chrisdalke/pumpkin-carving-robot/hardware/z_axis_400mm.SLDPRT

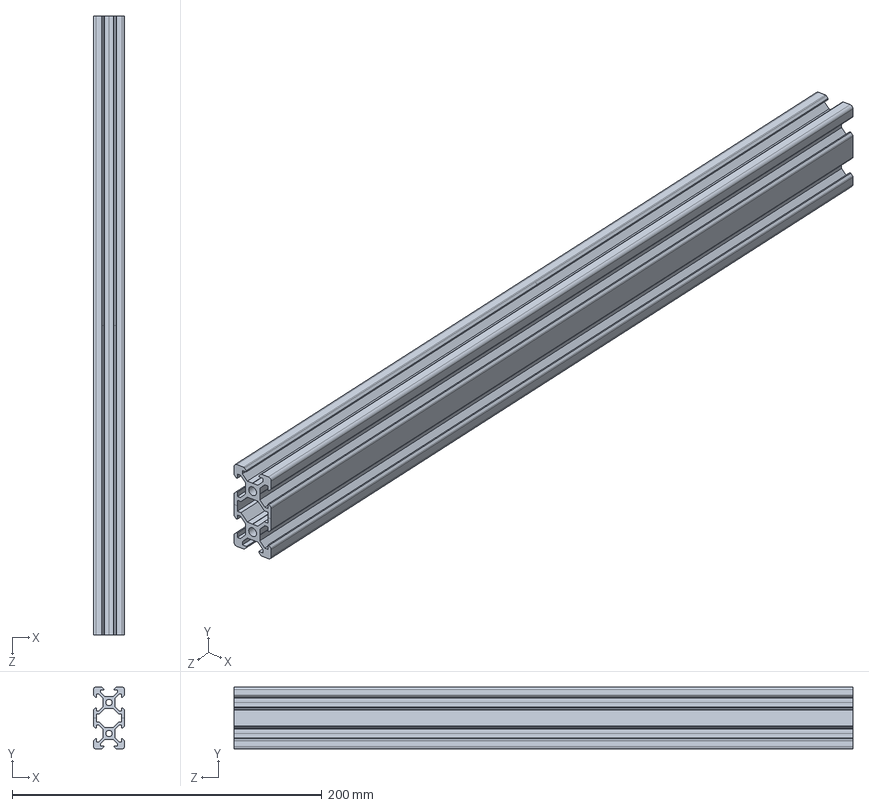
[picture p19: CAD file, 2022-10-28]
hardware/z_axis_400mm.SLDPRT
20.0 x 40.0 x 400.0 mm
