chrisdalke/pumpkin-carving-robot/hardware/8020/8020-1010-BLACK X 8.SLDPRT

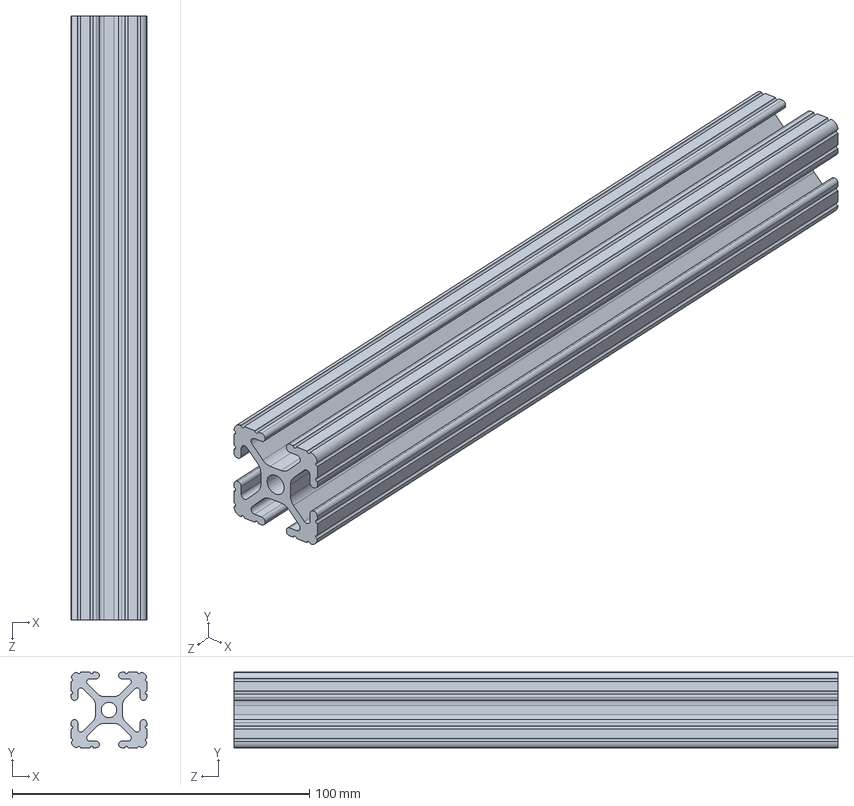
[picture p20: CAD file, 2021-10-21]
hardware/8020/8020-1010-BLACK X 8.SLDPRT
25.4 x 25.4 x 203.2 mm
