chrisdalke/pumpkin-carving-robot/hardware/v_slot_12in.SLDPRT

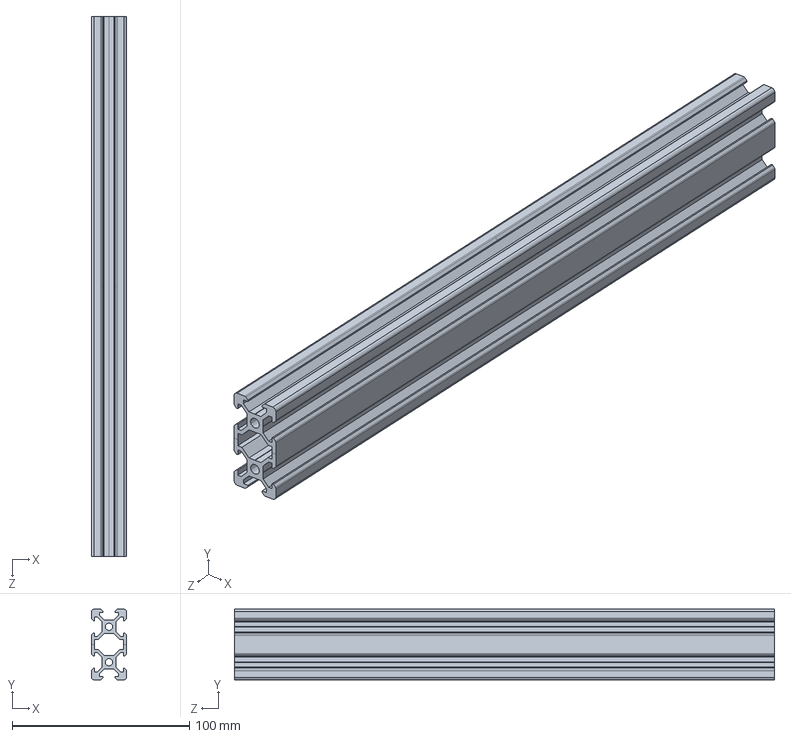
[picture p21: CAD file, 2022-10-28]
hardware/v_slot_12in.SLDPRT
20.0 x 40.0 x 304.8 mm
