chrisdalke/pumpkin-carving-robot/hardware/775 Holder v1.SLDPRT

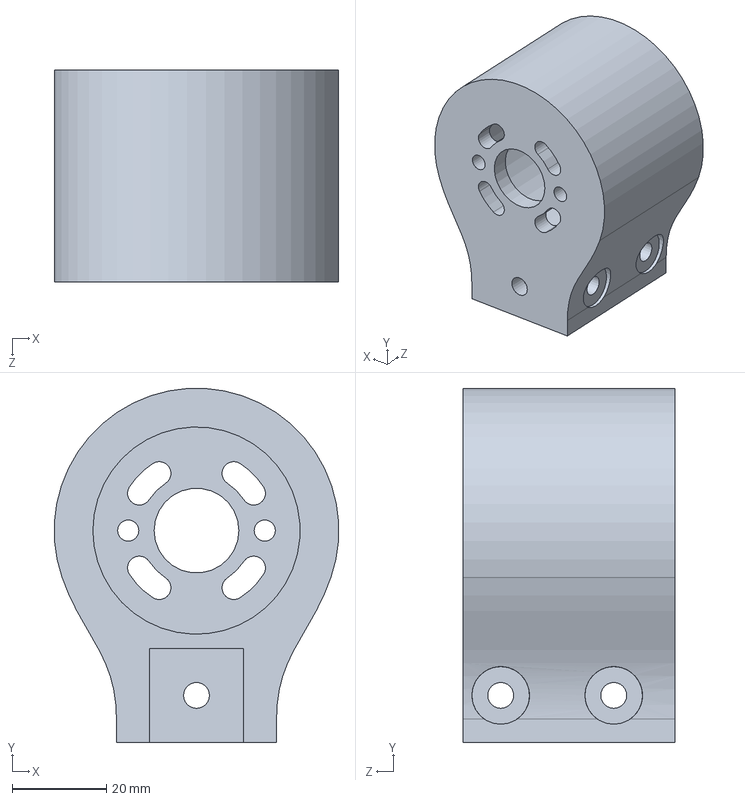
[picture p22: CAD file, 2022-10-28]
hardware/775 Holder v1.SLDPRT
60.4 x 75.2 x 45.0 mm
