chrisdalke/pumpkin-carving-robot/hardware/8020/8020-1010-BLACK X 22.SLDPRT

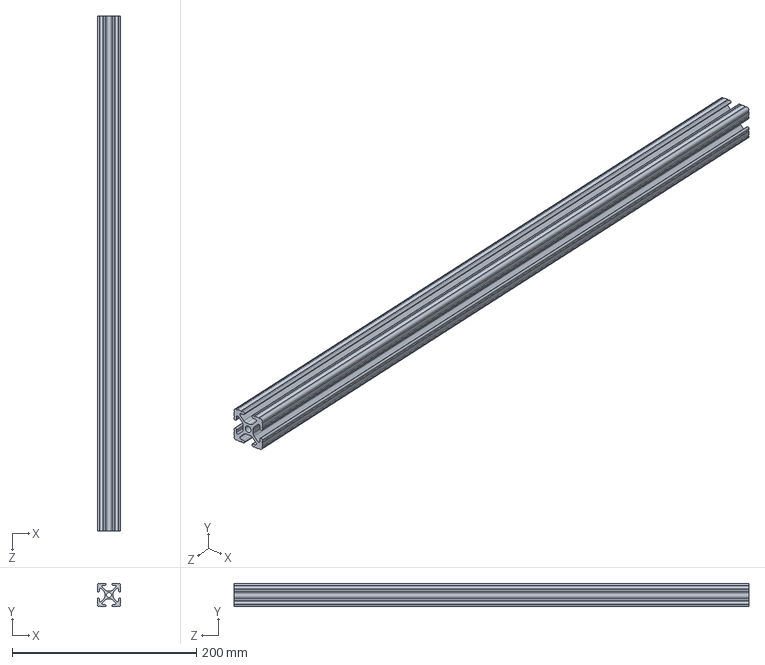
[picture p23: CAD file, 2021-10-21]
hardware/8020/8020-1010-BLACK X 22.SLDPRT
25.4 x 25.4 x 558.8 mm
