chrisdalke/pumpkin-carving-robot/hardware/8020/8020-1010-BLACK X 18.SLDPRT

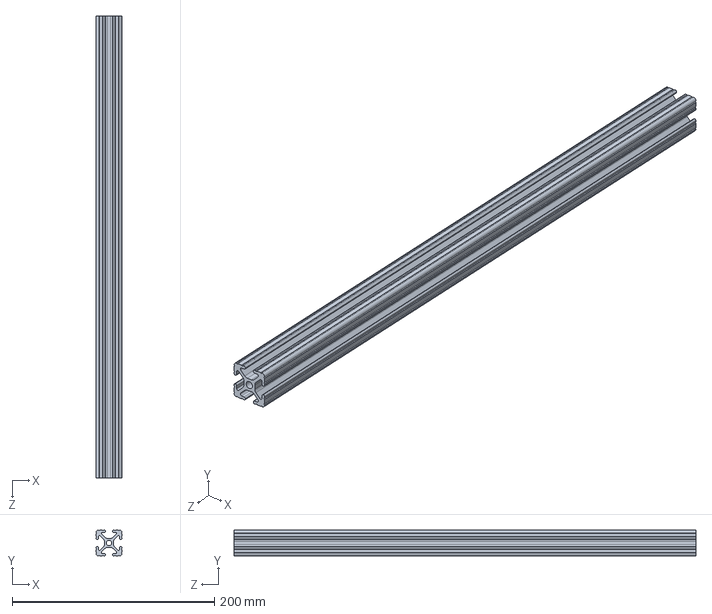
[picture p24: CAD file, 2021-10-21]
hardware/8020/8020-1010-BLACK X 18.SLDPRT
25.4 x 25.4 x 457.2 mm
