chrisdalke/pumpkin-carving-robot/hardware/z_limit_bracket.SLDPRT

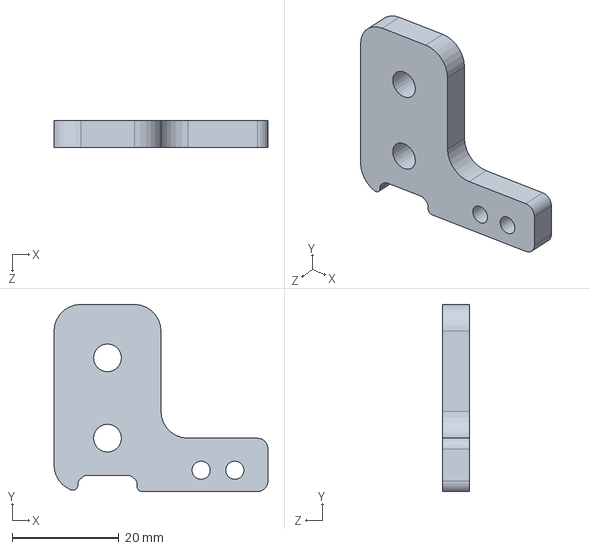
[picture p25: CAD file, 2022-10-28]
hardware/z_limit_bracket.SLDPRT
40.0 x 35.0 x 5.00 mm
