chrisdalke/pumpkin-carving-robot/hardware/8020/8020-20-2040 X 0_254 M.SLDPRT

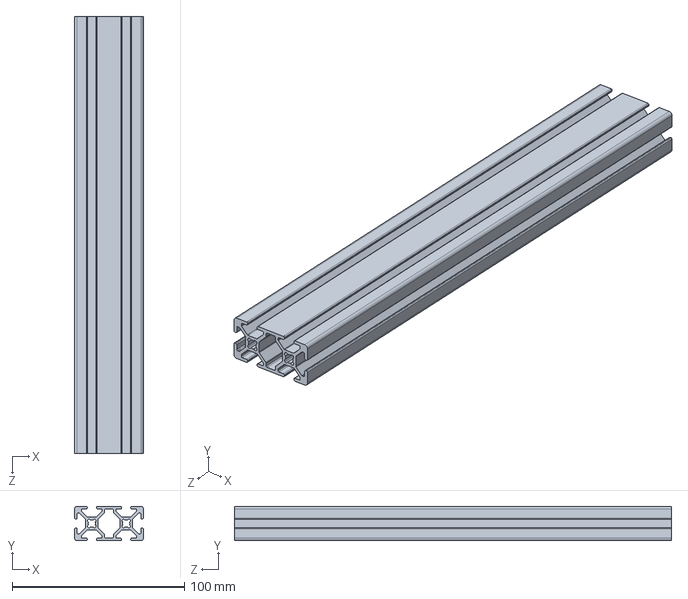
[picture p26: CAD file, 2021-10-21]
hardware/8020/8020-20-2040 X 0_254 M.SLDPRT
40.0 x 20.0 x 254.0 mm
