chrisdalke/pumpkin-carving-robot/hardware/z_bearing_bracket.SLDPRT

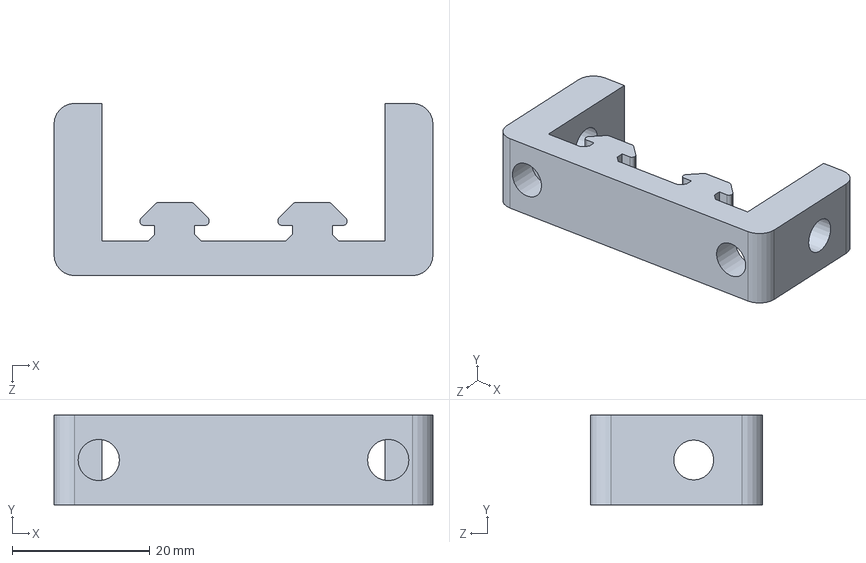
[picture p27: CAD file, 2022-10-28]
hardware/z_bearing_bracket.SLDPRT
55.0 x 13.0 x 25.0 mm
