chrisdalke/pumpkin-carving-robot/hardware/8020/8020-1010-BLACK X 20.SLDPRT

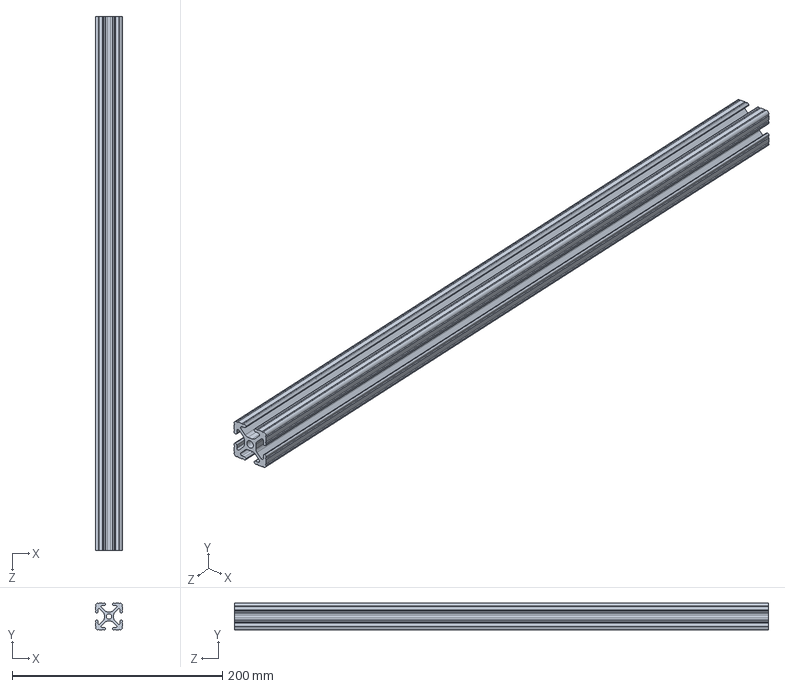
[picture p28: CAD file, 2021-10-21]
hardware/8020/8020-1010-BLACK X 20.SLDPRT
25.4 x 25.4 x 508.0 mm
