chrisdalke/pumpkin-carving-robot/hardware/gantry_anchor.SLDPRT

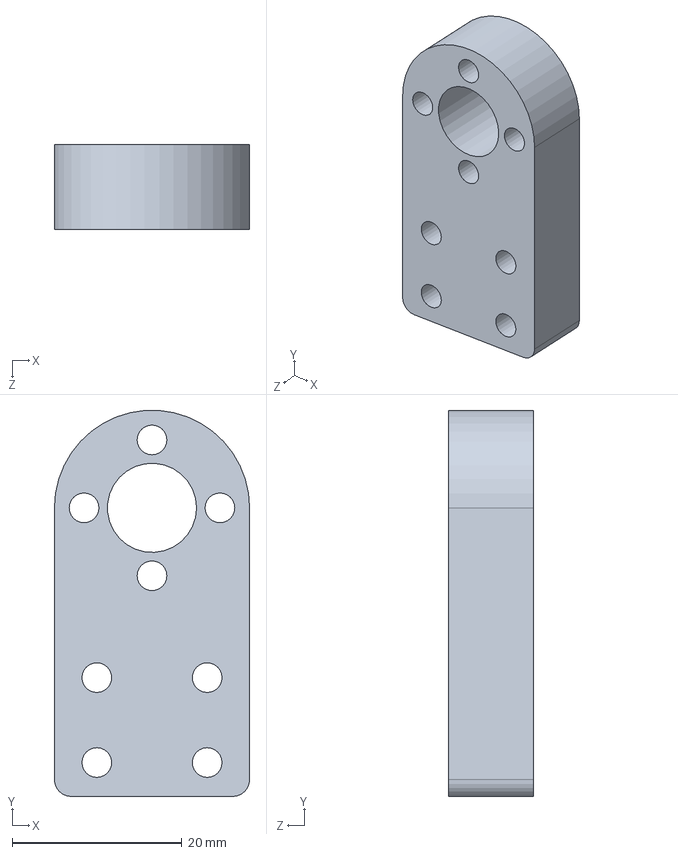
[picture p29: CAD file, 2022-10-28]
hardware/gantry_anchor.SLDPRT
23.0 x 45.5 x 10.0 mm
