chrisdalke/pumpkin-carving-robot/hardware/driver_mount.SLDPRT

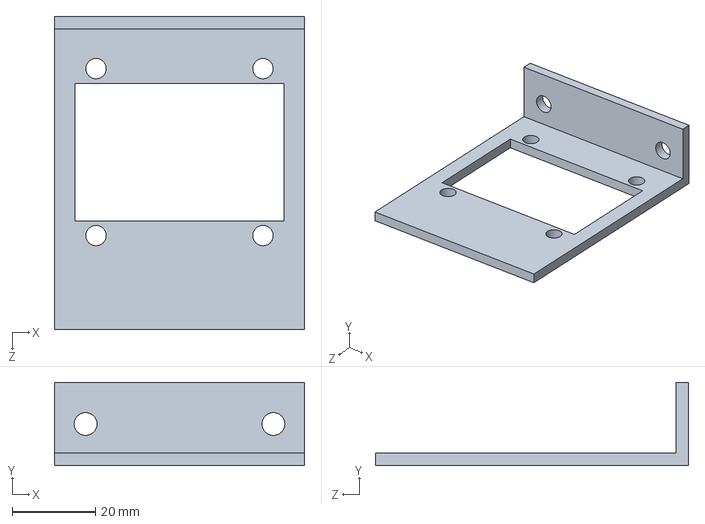
[picture p30: CAD file, 2022-10-28]
hardware/driver_mount.SLDPRT
60.0 x 20.0 x 75.0 mm
