chrisdalke/pumpkin-carving-robot/hardware/table spacer.SLDPRT

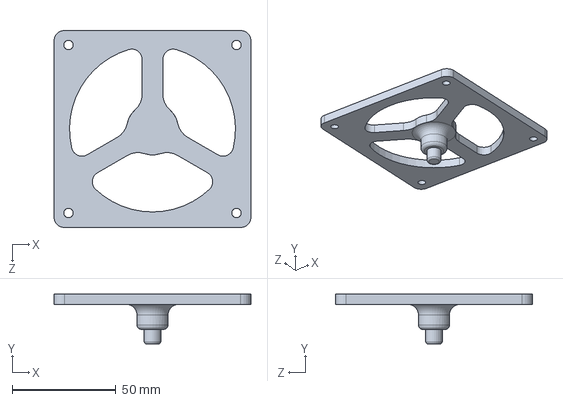
[picture p31: CAD file, 2022-10-28]
hardware/table spacer.SLDPRT
95.0 x 24.0 x 95.0 mm
