chrisdalke/pumpkin-carving-robot/hardware/coupler.SLDPRT

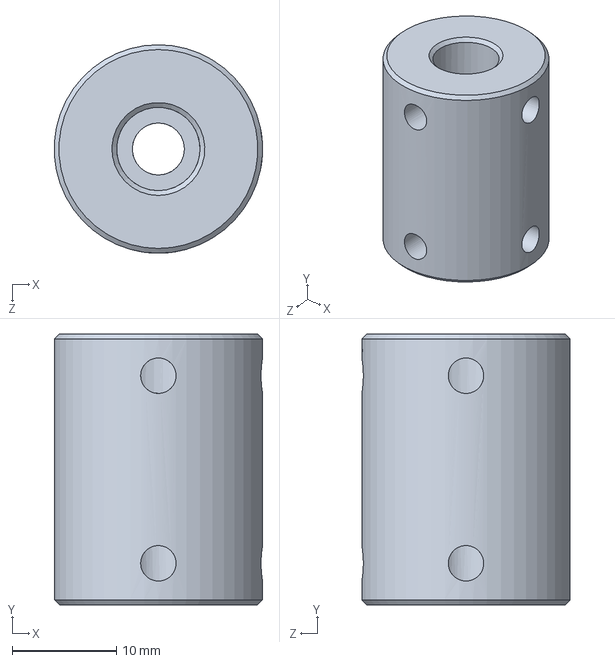
[picture p32: CAD file, 2022-10-28]
hardware/coupler.SLDPRT
20.0 x 26.0 x 20.0 mm
