chrisdalke/pumpkin-carving-robot/hardware/gantry_stepper_bracket.SLDPRT

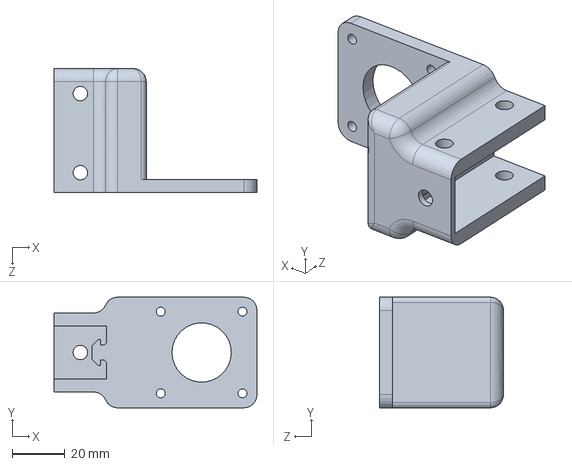
[picture p33: CAD file, 2022-10-28]
hardware/gantry_stepper_bracket.SLDPRT
77.0 x 42.0 x 47.0 mm
