chrisdalke/pumpkin-carving-robot/hardware/tof_bracket.SLDPRT

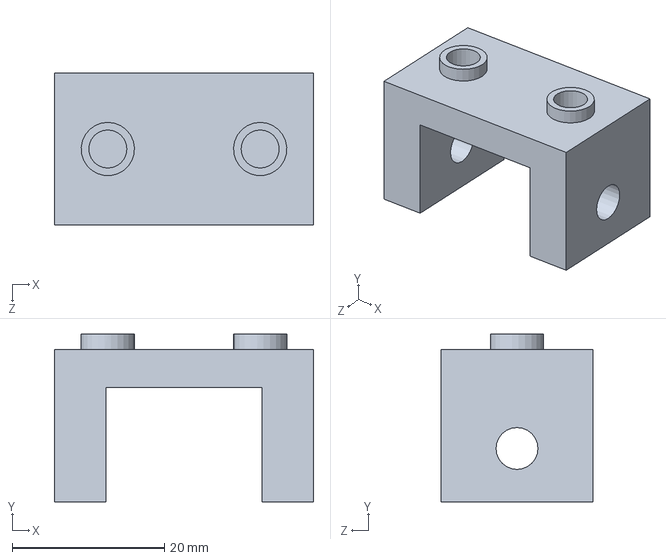
[picture p34: CAD file, 2022-10-28]
hardware/tof_bracket.SLDPRT
34.0 x 22.0 x 20.0 mm
