chrisdalke/pumpkin-carving-robot/hardware/electronics_mount.SLDPRT

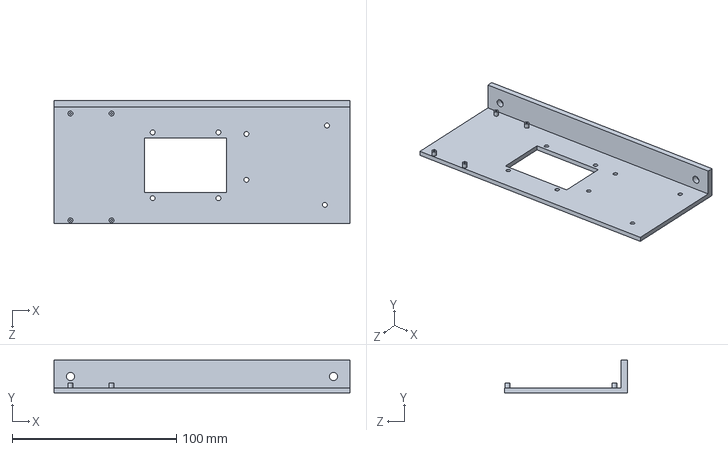
[picture p35: CAD file, 2022-10-28]
hardware/electronics_mount.SLDPRT
180.0 x 20.0 x 75.0 mm
