chrisdalke/pumpkin-carving-robot/hardware/z_motor_bracket.SLDPRT

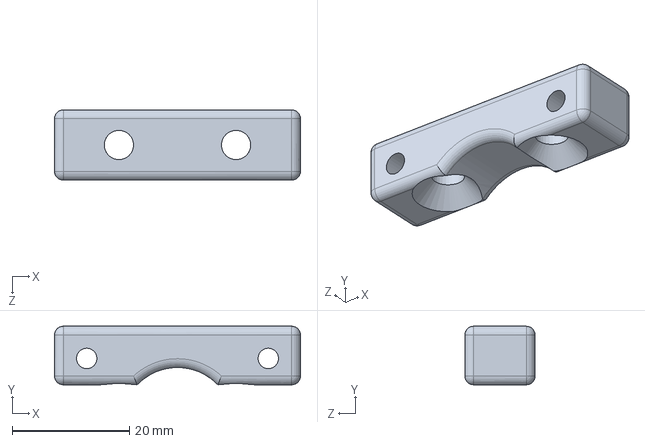
[picture p36: CAD file, 2022-10-28]
hardware/z_motor_bracket.SLDPRT
42.0 x 10.0 x 12.0 mm
