chrisdalke/pumpkin-carving-robot/hardware/z_cap.SLDPRT

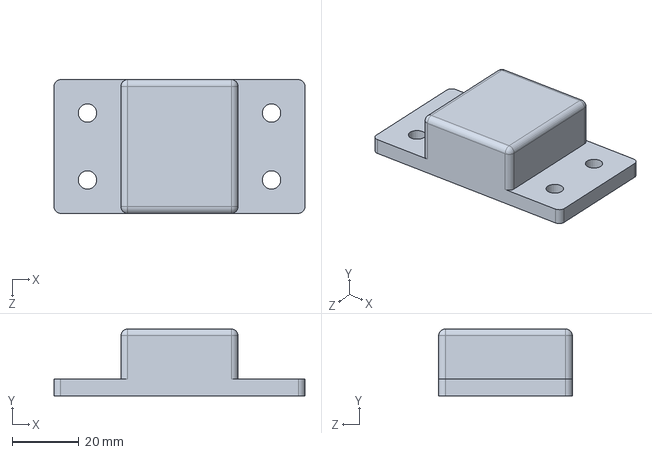
[picture p37: CAD file, 2022-10-28]
hardware/z_cap.SLDPRT
75.0 x 20.0 x 40.0 mm
