chrisdalke/pumpkin-carving-robot/hardware/roller.SLDPRT

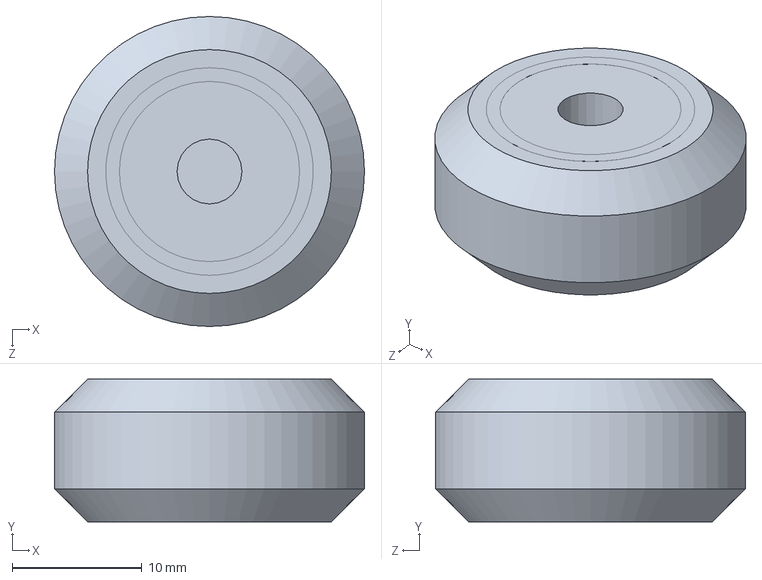
[picture p38: CAD file, 2022-10-28]
hardware/roller.SLDPRT
23.9 x 11.0 x 23.9 mm
