chrisdalke/pumpkin-carving-robot/hardware/z axis mount 1.SLDPRT

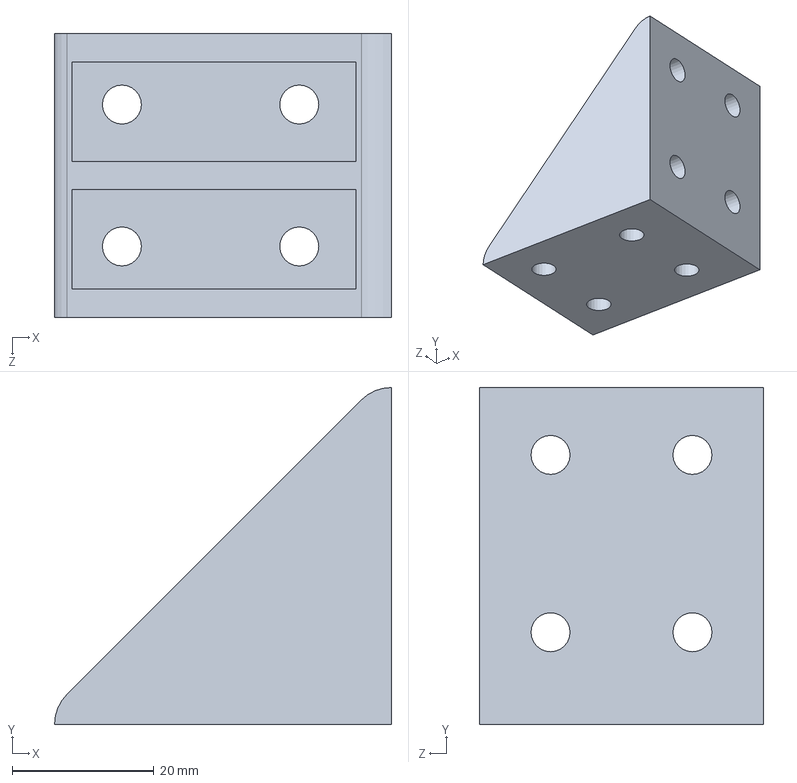
[picture p39: CAD file, 2022-10-28]
hardware/z axis mount 1.SLDPRT
47.5 x 47.5 x 40.0 mm
