chrisdalke/pumpkin-carving-robot/hardware/z_axis_bracket.SLDPRT

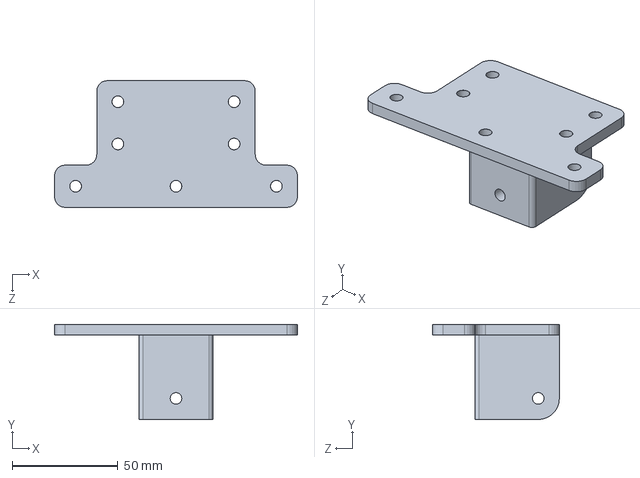
[picture p40: CAD file, 2022-10-28]
hardware/z_axis_bracket.SLDPRT
115.0 x 45.0 x 60.0 mm
