chrisdalke/pumpkin-carving-robot/hardware/z_carriage_flat.SLDPRT

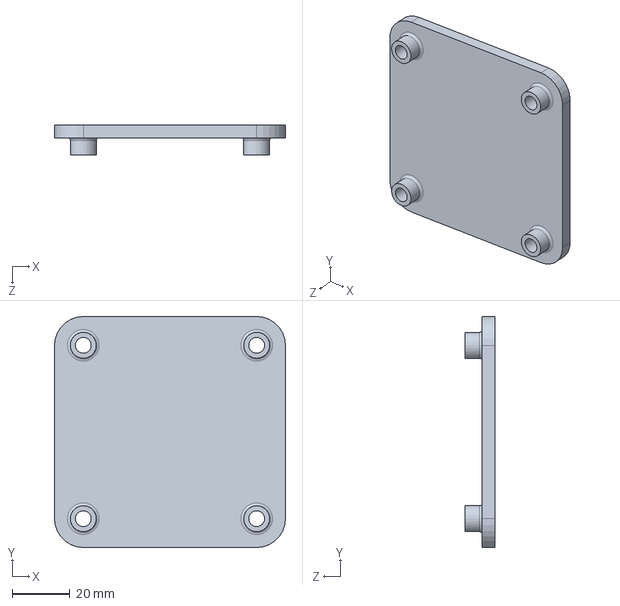
[picture p41: CAD file, 2022-10-28]
hardware/z_carriage_flat.SLDPRT
80.2 x 80.2 x 10.5 mm
