chrisdalke/pumpkin-carving-robot/hardware/shield_mount.SLDPRT

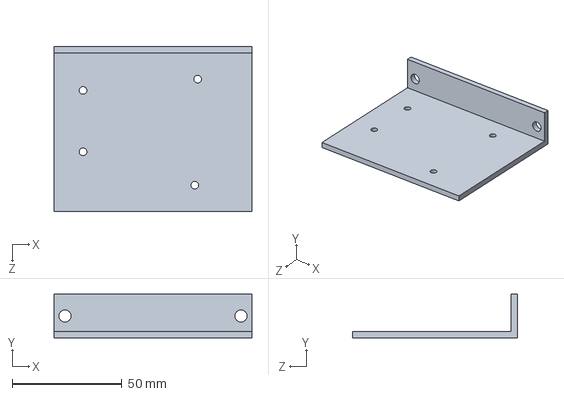
[picture p42: CAD file, 2022-10-28]
hardware/shield_mount.SLDPRT
90.0 x 20.0 x 75.0 mm
