chrisdalke/pumpkin-carving-robot/hardware/calibrator_mount.SLDPRT

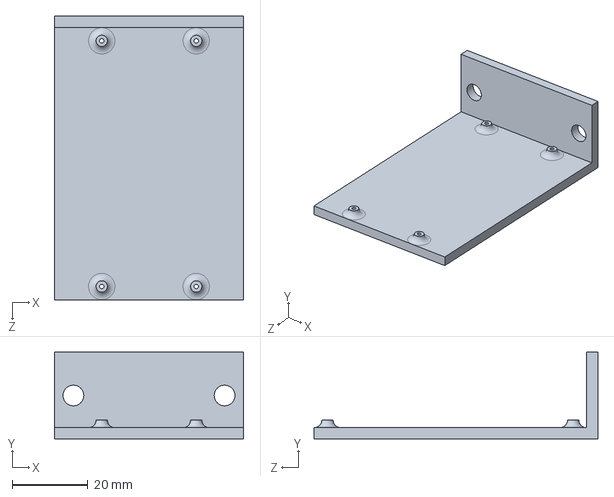
[picture p43: CAD file, 2022-10-28]
hardware/calibrator_mount.SLDPRT
50.0 x 23.0 x 75.0 mm
