chrisdalke/pumpkin-carving-robot/hardware/Swivel gear mount.SLDPRT

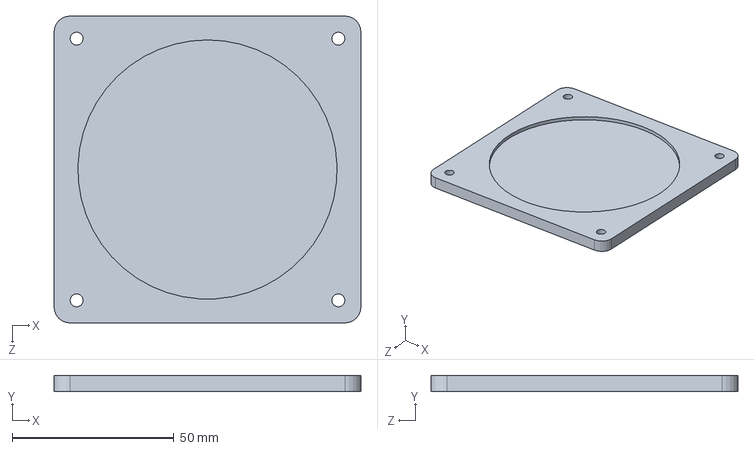
[picture p44: CAD file, 2021-10-26]
hardware/Swivel gear mount.SLDPRT
95.0 x 5.00 x 95.0 mm
