chrisdalke/pumpkin-carving-robot/hardware/swivel nail mount.SLDPRT

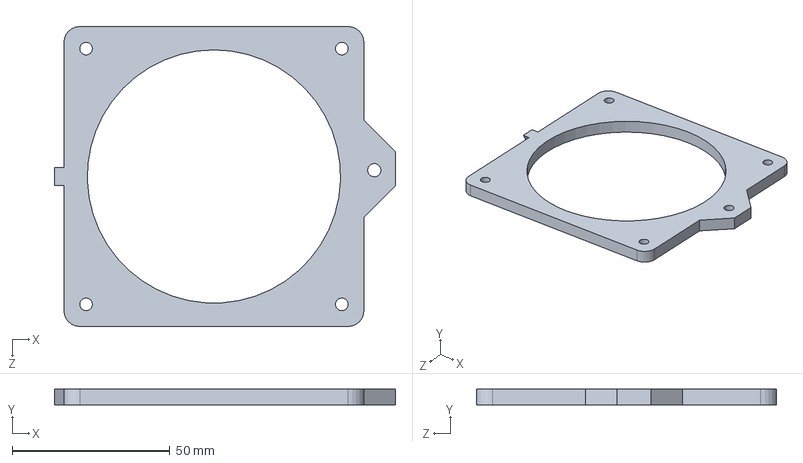
[picture p45: CAD file, 2021-10-26]
hardware/swivel nail mount.SLDPRT
108.0 x 5.00 x 95.0 mm
