chrisdalke/pumpkin-carving-robot/hardware/psu mount.SLDPRT

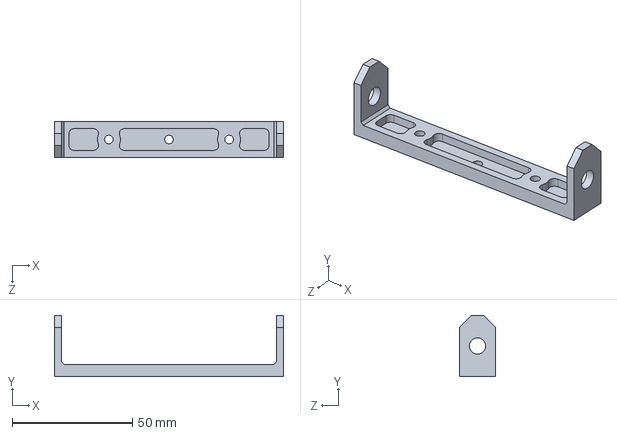
[picture p46: CAD file, 2021-10-26]
hardware/psu mount.SLDPRT
95.2 x 25.4 x 15.0 mm
