chrisdalke/pumpkin-carving-robot/hardware/power plug panel.SLDPRT

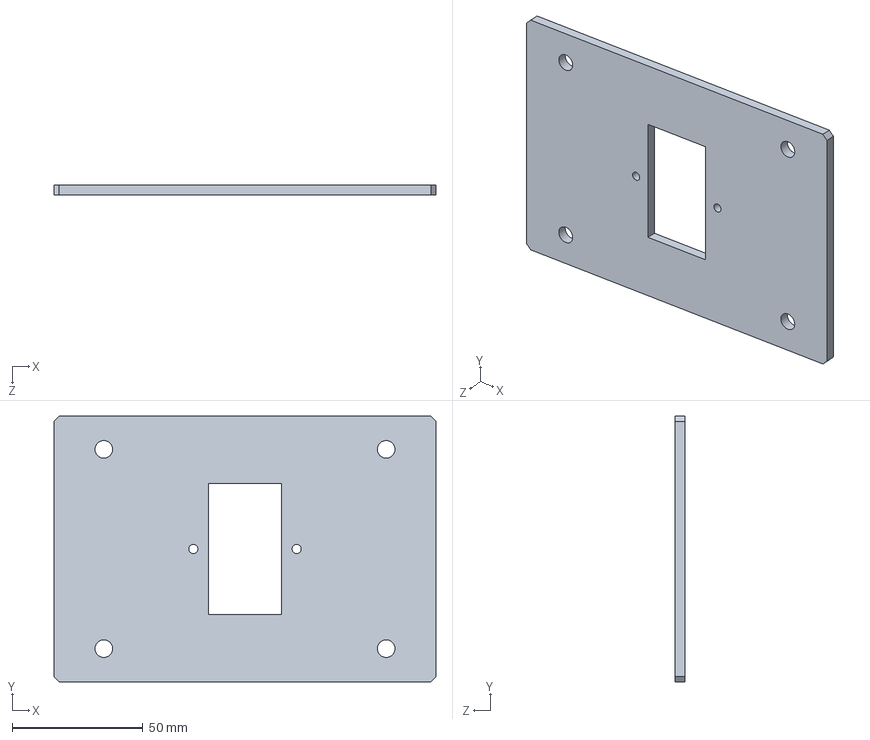
[picture p47: CAD file, 2021-10-25]
hardware/power plug panel.SLDPRT
146.1 x 101.6 x 4.00 mm
