chrisdalke/pumpkin-carving-robot/hardware/metric-to-imperial 8020 mount.SLDPRT

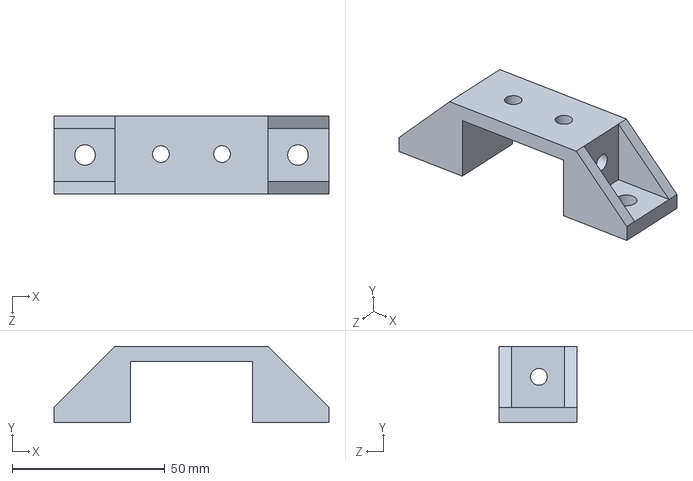
[picture p48: CAD file, 2021-10-25]
hardware/metric-to-imperial 8020 mount.SLDPRT
90.0 x 25.0 x 25.4 mm
