chrisdalke/pumpkin-carving-robot/hardware/foot.SLDPRT

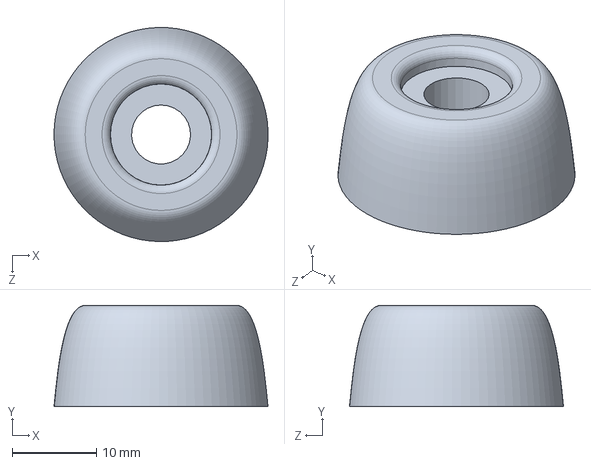
[picture p49: CAD file, 2021-10-25]
hardware/foot.SLDPRT
25.4 x 12.0 x 25.4 mm
