chrisdalke/pumpkin-carving-robot/hardware/PSU placeholder.SLDPRT

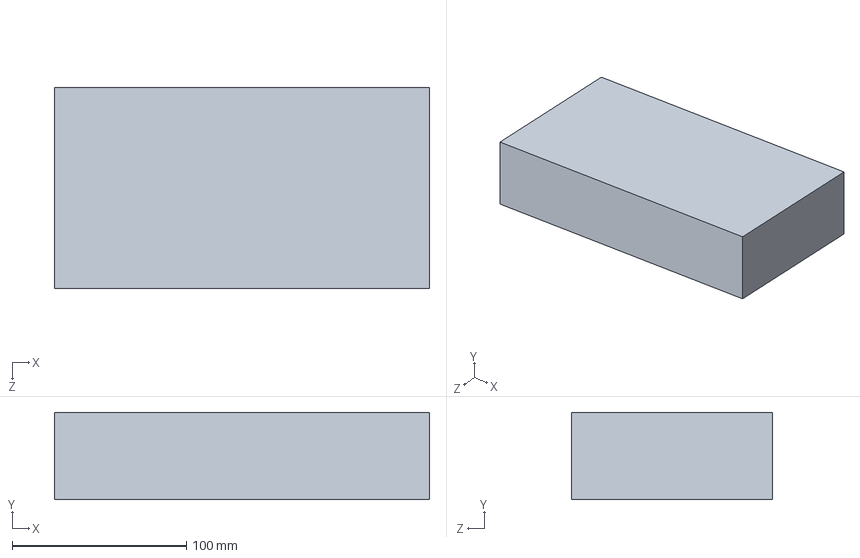
[picture p50: CAD file, 2021-10-25]
hardware/PSU placeholder.SLDPRT
215.0 x 50.0 x 115.0 mm
