chrisdalke/pumpkin-carving-robot/hardware/pumpkin holder v2.SLDPRT

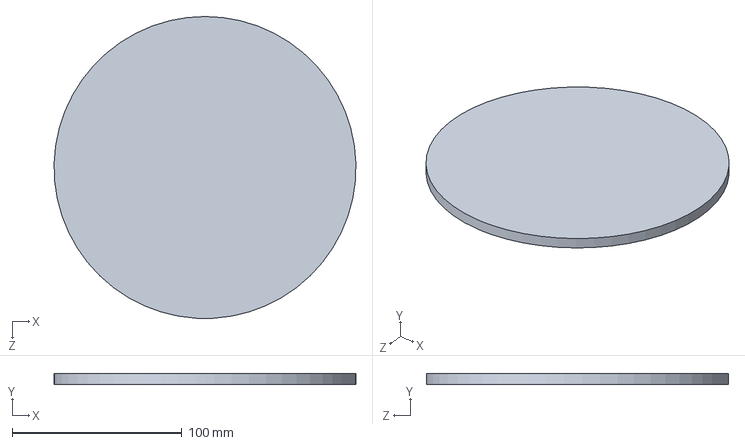
[picture p51: CAD file, 2021-10-21]
hardware/pumpkin holder v2.SLDPRT
177.7 x 6.35 x 177.8 mm
