chrisdalke/pumpkin-carving-robot/hardware/stepper spur gear.SLDPRT

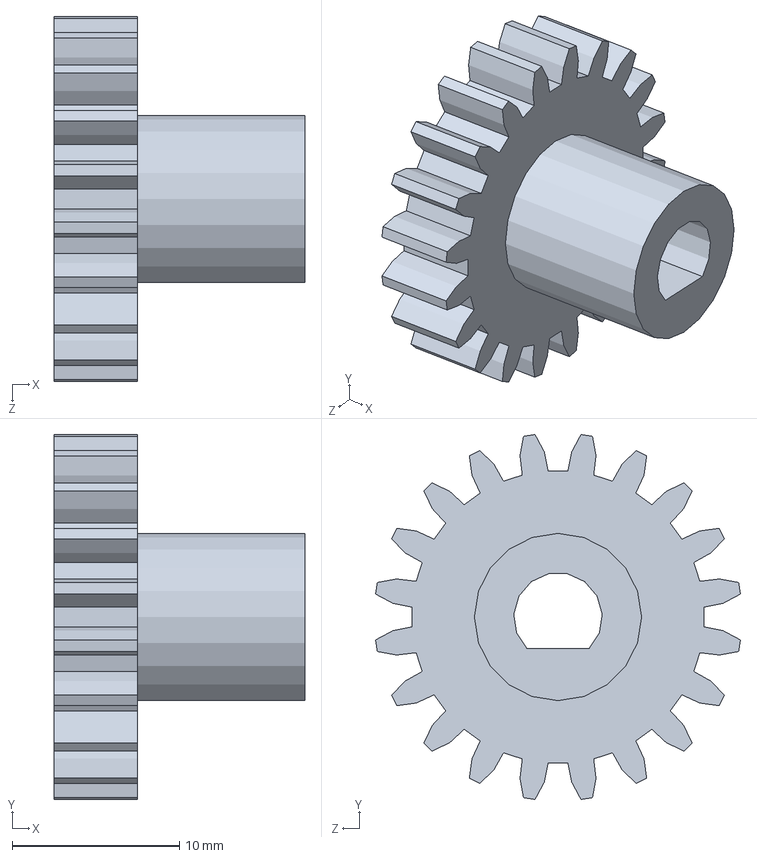
[picture p52: CAD file, 2021-10-18]
hardware/stepper spur gear.SLDPRT
15.0 x 21.8 x 21.8 mm
