chrisdalke/pumpkin-carving-robot/hardware/spacer.SLDPRT

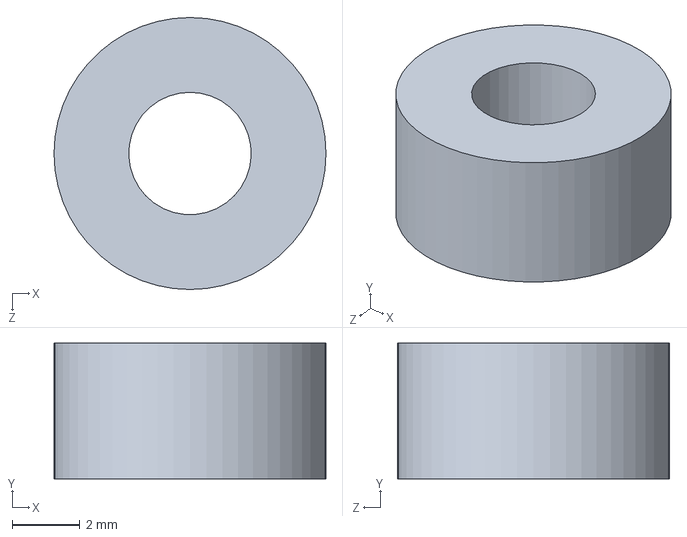
[picture p53: CAD file, 2021-10-18]
hardware/spacer.SLDPRT
8.00 x 4.00 x 8.00 mm
