chrisdalke/pumpkin-carving-robot/hardware/swivel base.SLDPRT

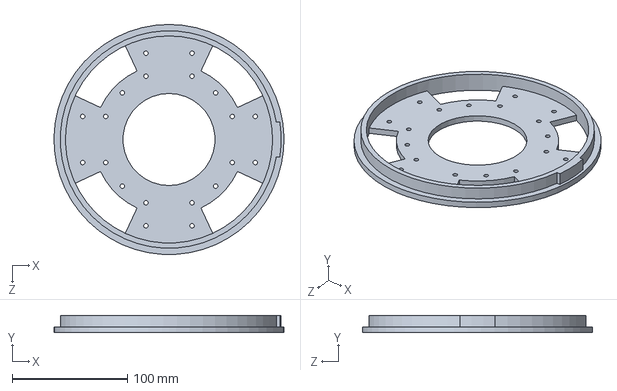
[picture p54: CAD file, 2021-10-10]
hardware/swivel base.SLDPRT
199.9 x 15.0 x 200.0 mm
