chrisdalke/pumpkin-carving-robot/hardware/internal spur gear_am 3.SLDPRT

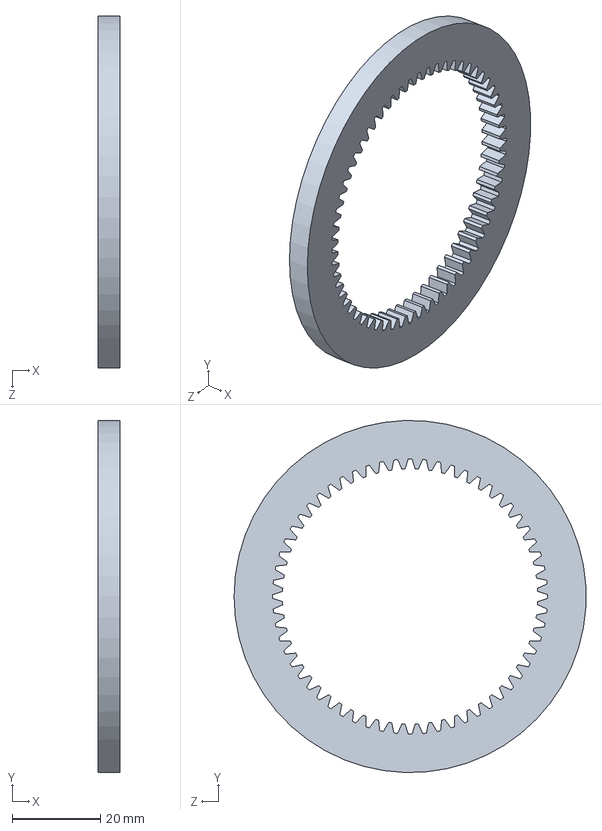
[picture p55: CAD file, 2021-10-10]
hardware/internal spur gear_am 3.SLDPRT
5.00 x 80.0 x 79.9 mm
