chrisdalke/pumpkin-carving-robot/hardware/Turntable base.SLDPRT

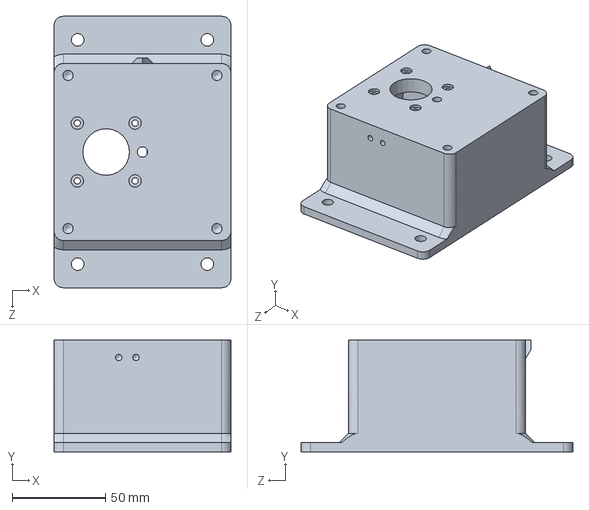
[picture p56: CAD file, 2021-10-10]
hardware/Turntable base.SLDPRT
95.0 x 60.0 x 145.8 mm
