chrisdalke/pumpkin-carving-robot/hardware/Swivel mockup.SLDPRT

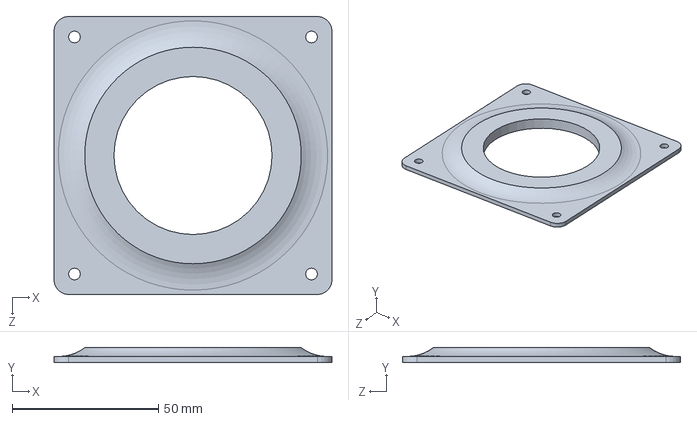
[picture p57: CAD file, 2021-10-10]
hardware/Swivel mockup.SLDPRT
95.0 x 5.00 x 95.0 mm
